ELCOche/ELCOche/Web Page/img/galery/DSC03420.JPG

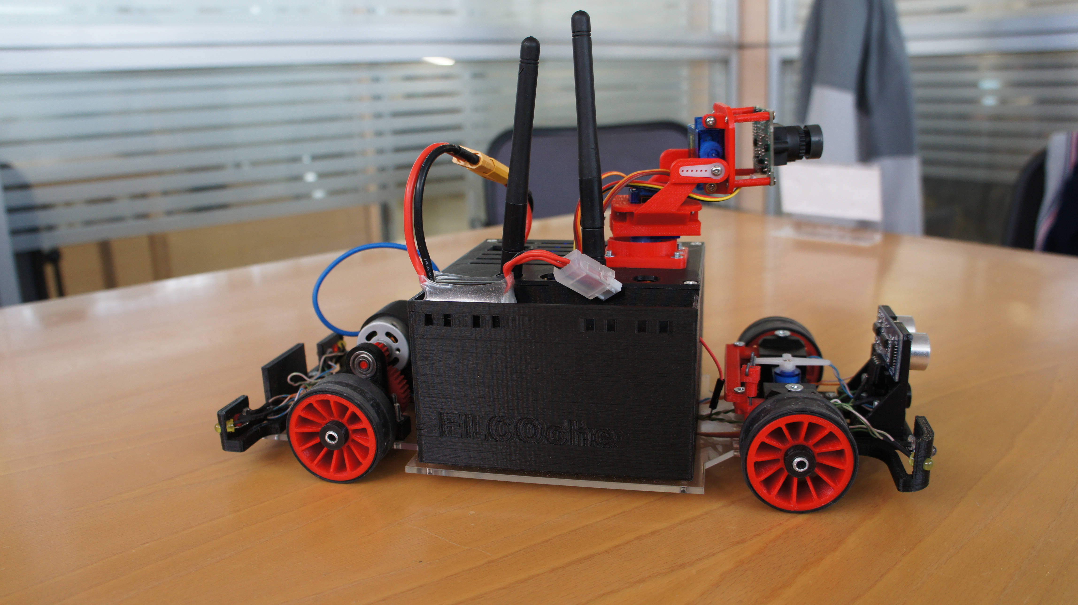
Web Page/img/galery/DSC03420.JPG
