ELCOche/ELCOche/Web Page/img/galery/DSC03431.JPG

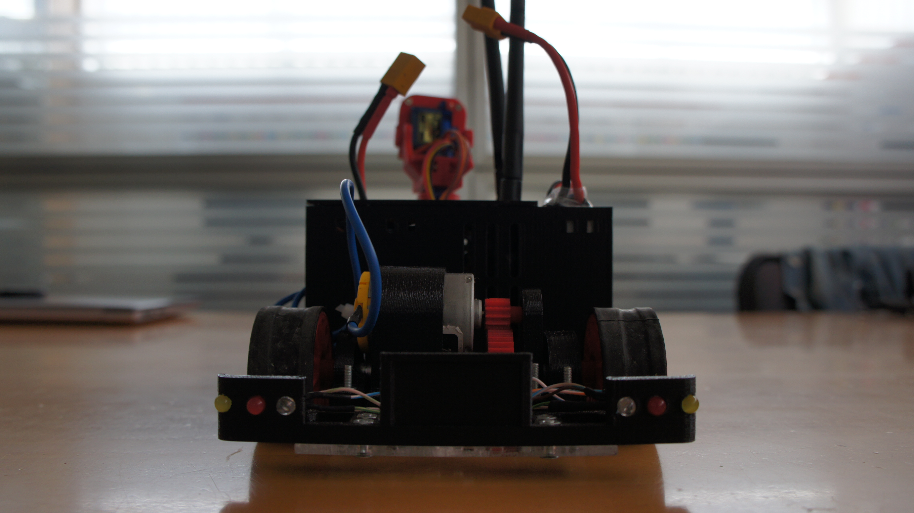
Web Page/img/galery/DSC03431.JPG
