ELCOche/ELCOche/Web Page/img/galery/DSC03433.JPG

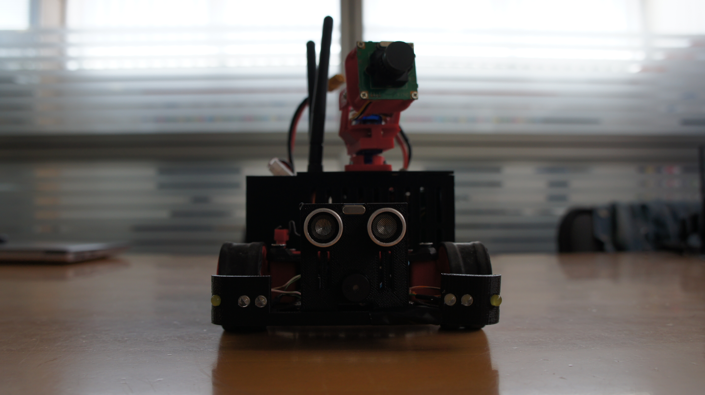
Web Page/img/galery/DSC03433.JPG
