ELCOche/ELCOche/Web Page/img/galery/DSC03434.JPG

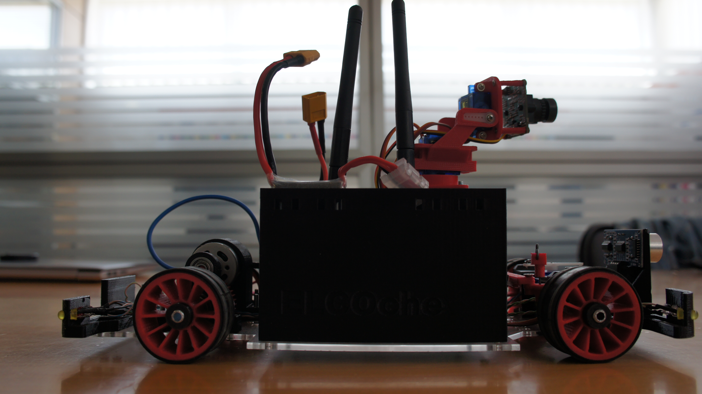
Web Page/img/galery/DSC03434.JPG
