ELCOche/ELCOche/Web Page/img/galery/img5.png

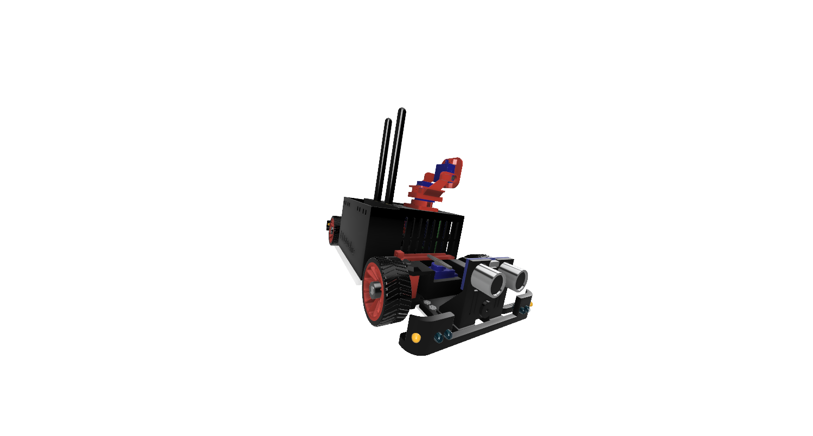
Web Page/img/galery/img5.png
