ELCOche/ELCOche/Web Page/img/galery/pedal_no_background.png

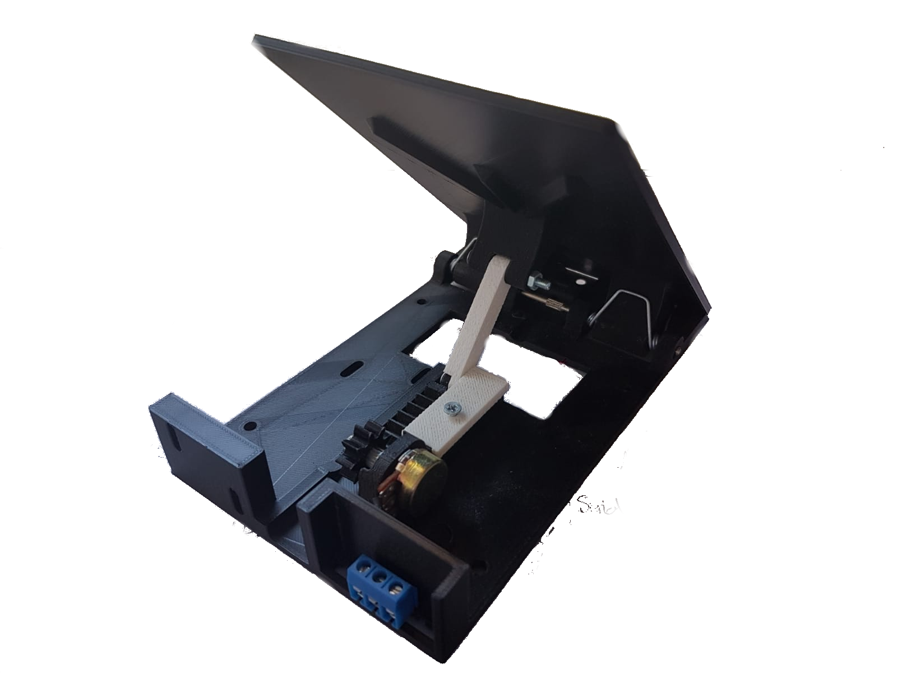
Web Page/img/galery/pedal_no_background.png
