ELCOche/ELCOche/STL archives for 3D printing/Steering wheel/muelles.stl

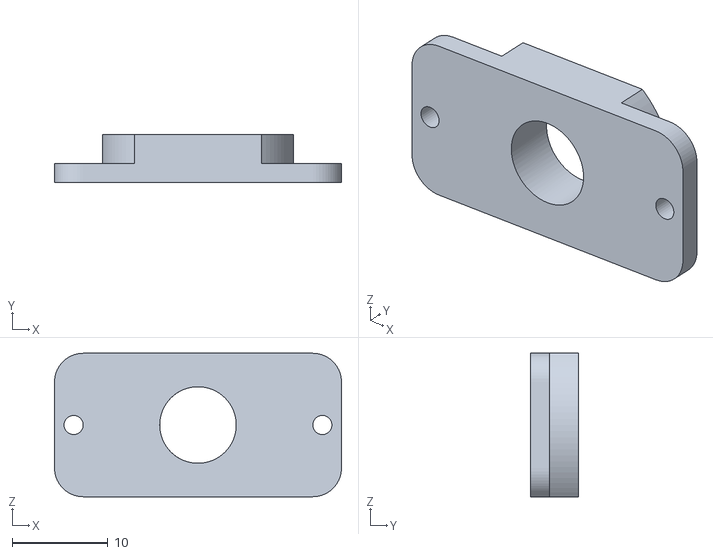
[picture p36: CAD file, 2019-05-10, an earlier design]
STL archives for 3D printing/Steering wheel/muelles.stl
30.0 x 5.00 x 15.0
