ELCOche/ELCOche/STL archives for 3D printing/Throttle/brazo.stl

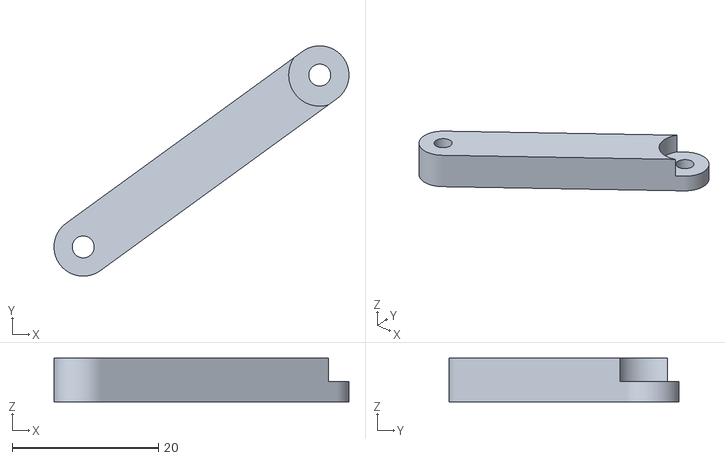
[picture p37: CAD file, 2019-05-10, an earlier design]
STL archives for 3D printing/Throttle/brazo.stl
40.4 x 31.5 x 6.00
