ELCOche/ELCOche/STL archives for 3D printing/Camera/brazo_izquierdo.stl

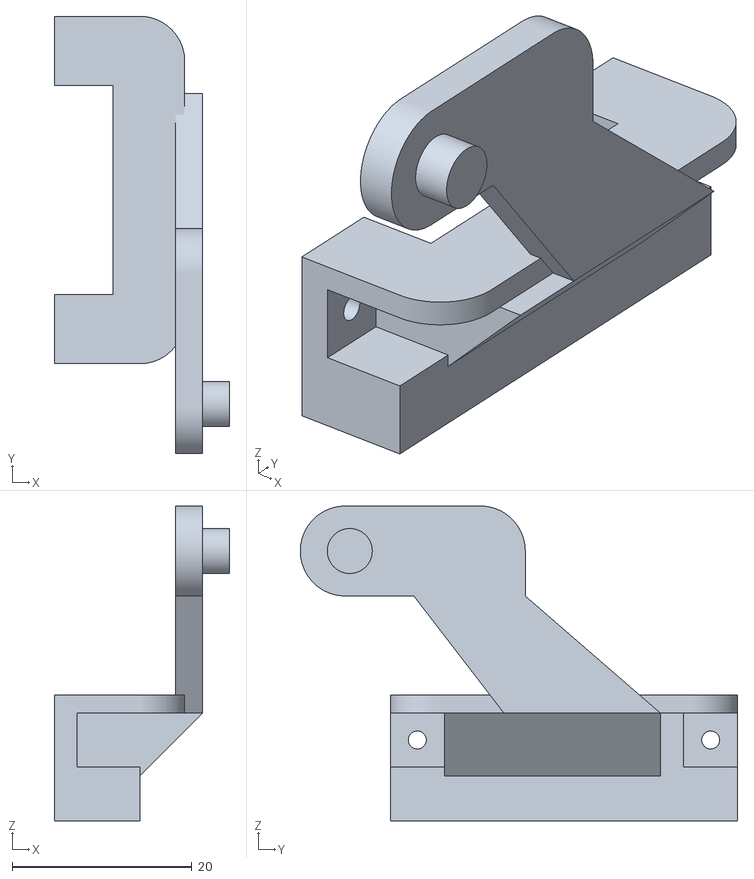
[picture p38: CAD file, 2019-05-10, an earlier design]
STL archives for 3D printing/Camera/brazo_izquierdo.stl
19.5 x 48.6 x 35.0
