ELCOche/ELCOche/STL archives for 3D printing/Car/tope_rueda.stl

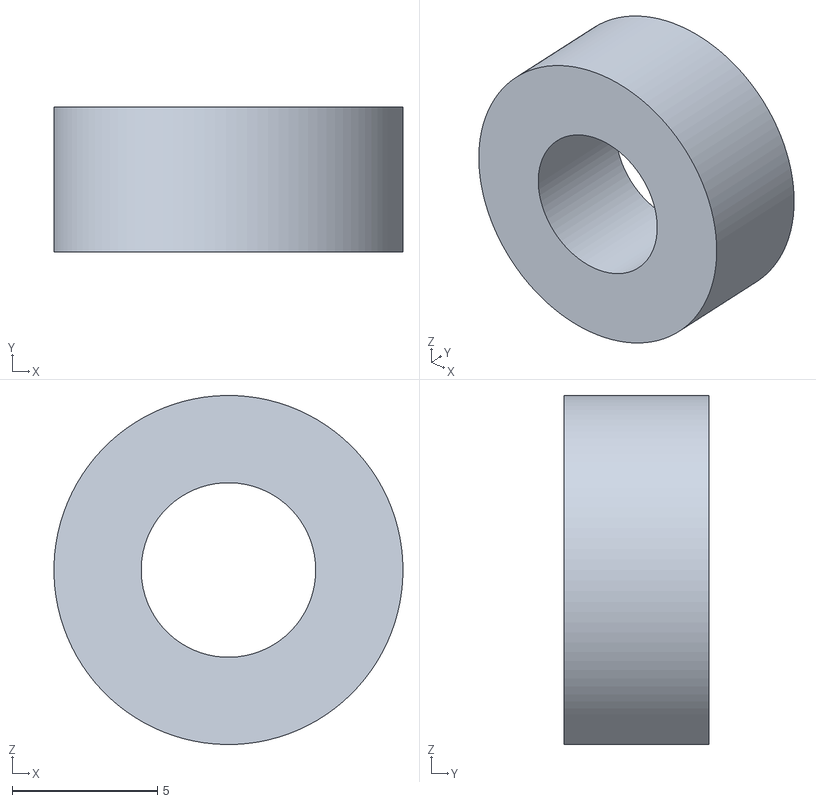
[picture p39: CAD file, 2019-05-10, an earlier design]
STL archives for 3D printing/Car/tope_rueda.stl
12.0 x 5.00 x 12.0
